bugcounting/nezoba/hw/pics/case_black_bottom_inside.jpg

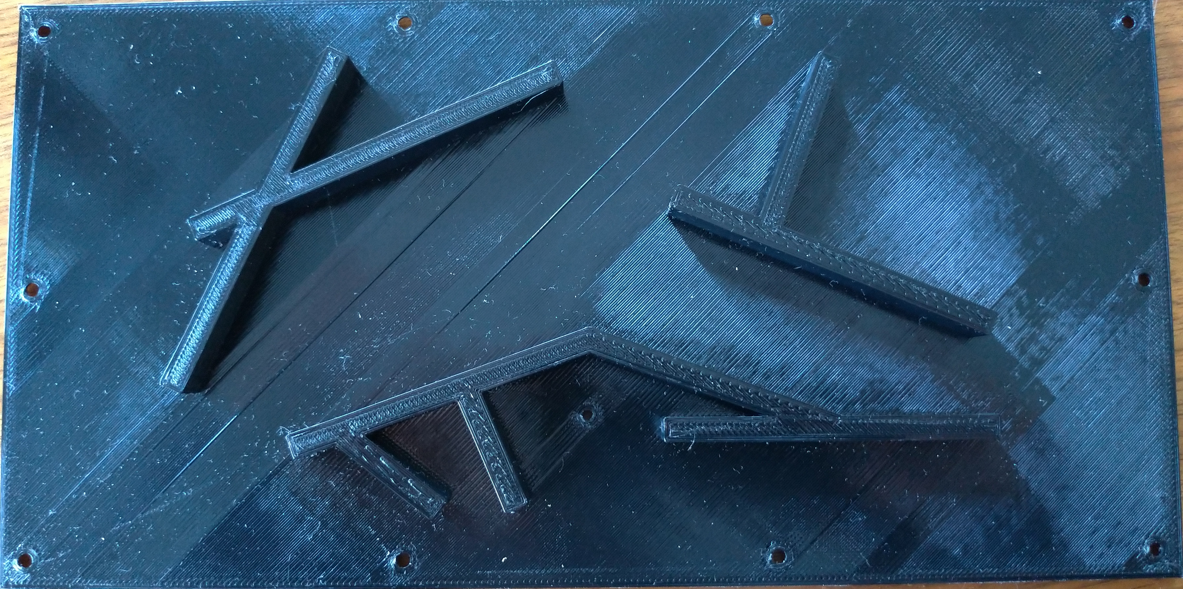
hw/pics/case_black_bottom_inside.jpg
