bugcounting/nezoba/hw/pics/case_black_bottom_outside.jpg

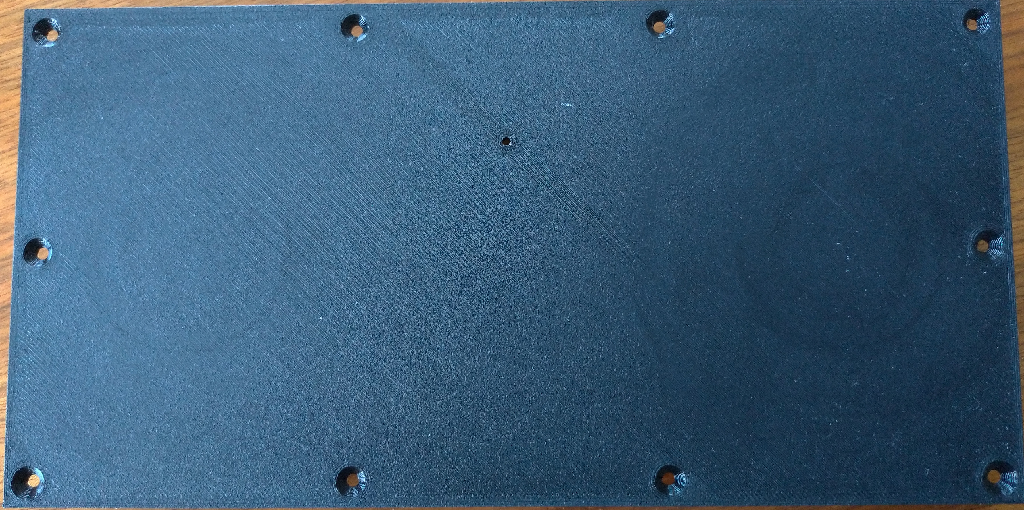
hw/pics/case_black_bottom_outside.jpg
