bugcounting/nezoba/hw/pics/case_orange_bottom_inside.jpg

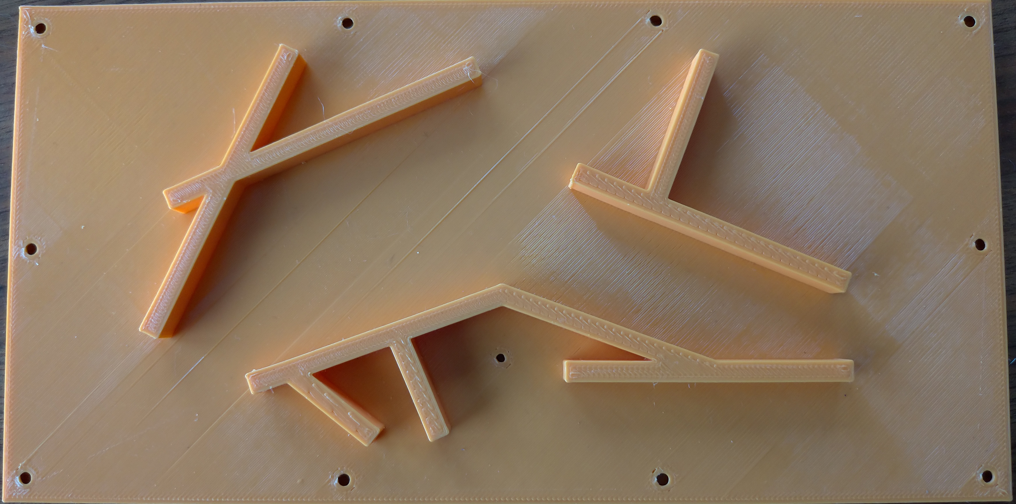
hw/pics/case_orange_bottom_inside.jpg
