bugcounting/nezoba/hw/pics/case_orange_top_inside.jpg

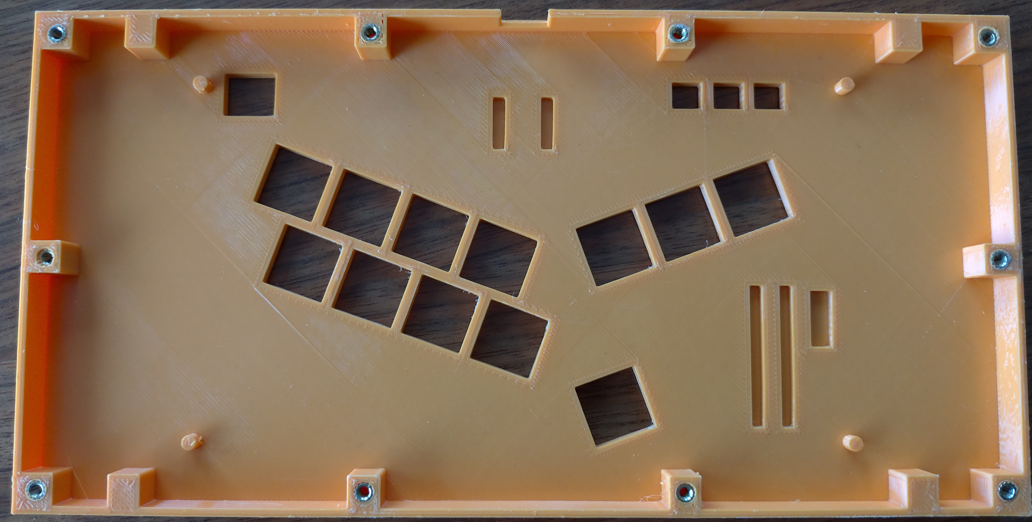
hw/pics/case_orange_top_inside.jpg
