bugcounting/nezoba/hw/pics/case_orange_top_outside.jpg

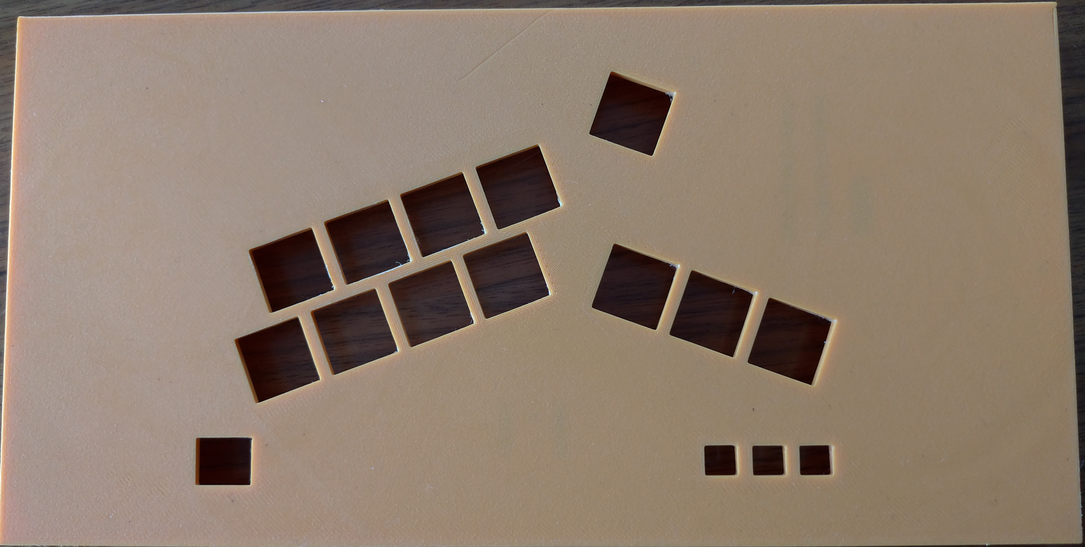
hw/pics/case_orange_top_outside.jpg
