bugcounting/nezoba/hw/pics/NezOba_orange_front.jpg

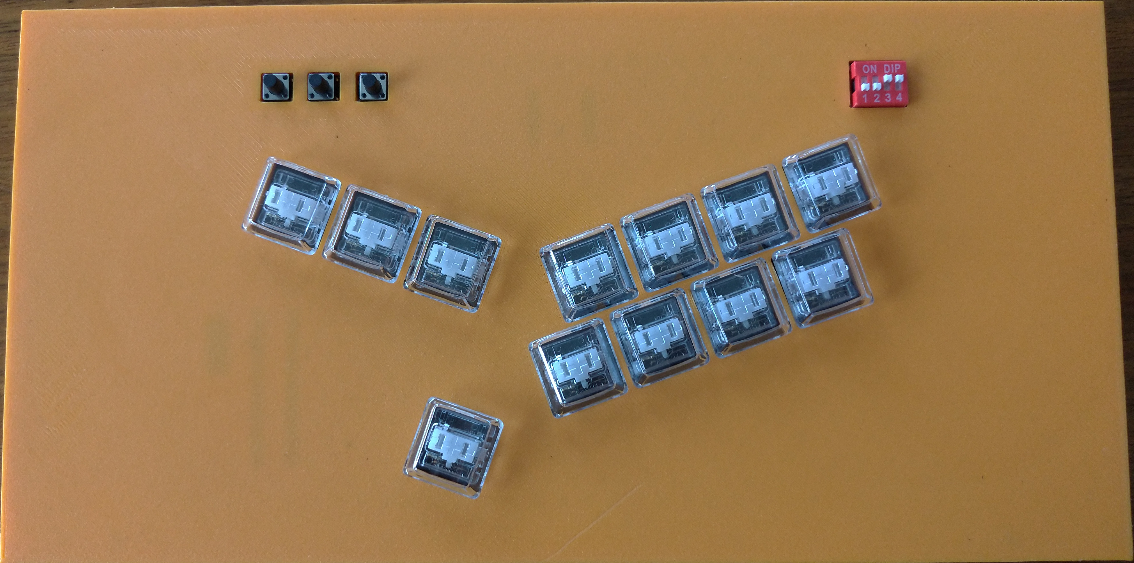
hw/pics/NezOba_orange_front.jpg
