bugcounting/nezoba/hw/pics/PCB_back.jpg

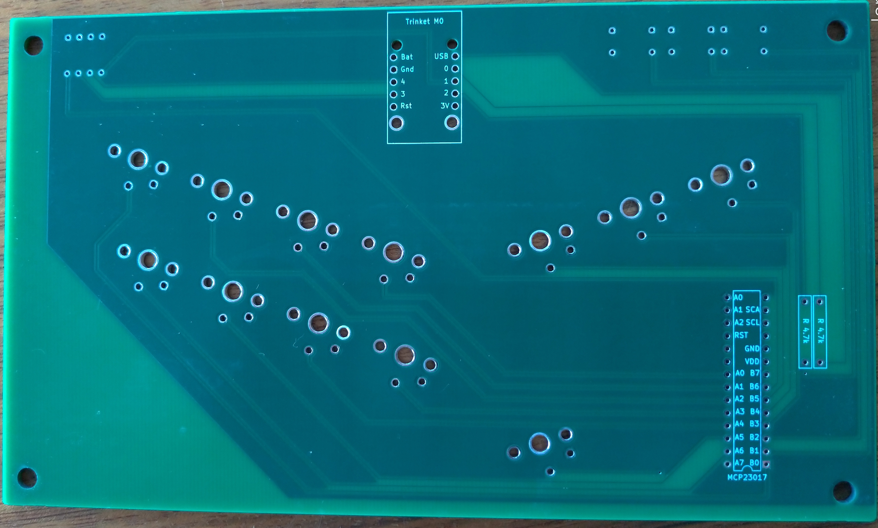
hw/pics/PCB_back.jpg
