bugcounting/nezoba/src/board/remap00.h

/*
  SMM2 standard: Index finger on run (Y), middle finger on jump (B);
  you can choose whether you prefer to spin jump with the thumb (L) or
  with the ring finger (R). Using the thumb should work better if you
  need to quickly switch between regular jumping and spin jumping. You
  can also use the lower row of keys (X, A, ZR), if you find a lower
  stance more comfortable.
*/

// NS
{
   /* ⇐ */       K_DP_LEFT,   K_NOOP,   K_NOOP,
   /* ⇓ */       K_DP_DOWN,   K_NOOP,   K_NOOP,
   /* ⇒ */      K_DP_RIGHT,   K_NOOP,   K_NOOP,
   /* ⇑ */         K_DP_UP,   K_NOOP,   K_NOOP,
   /* Y */             K_Y,   K_NOOP,   K_NOOP,
   /* B */             K_B,   K_NOOP,   K_NOOP,
   /* R */             K_R,   K_NOOP,   K_NOOP,
   /* ZL */           K_ZL,   K_NOOP,   K_NOOP,
   /* L */             K_L,   K_NOOP,   K_NOOP,
   /* X */             K_X,   K_NOOP,   K_NOOP,
   /* A */             K_A,   K_NOOP,   K_NOOP,
   /* ZR */           K_ZR,   K_NOOP,   K_NOOP,
   /* - */         K_MINUS,   K_NOOP,   K_NOOP,
   /* + */          K_PLUS,   K_NOOP,   K_NOOP,
   /* ⌂ */          K_HOME,   K_NOOP,   K_NOOP
}
