bugcounting/nezoba/src/board/remap01.h

/*
  SMM2 run on middle: A variant of "SMM2 standard" for those who
  prefer to use the middle finger to hold run (Y), while using the
  index finger to jump (B). The lower row is the same in "SMM2
  standard", so that you can try both schemes if you are on the fence
  about which one you prefer.
*/

// NS
{
   /* ⇐ */       K_DP_LEFT,   K_NOOP,   K_NOOP,
   /* ⇓ */       K_DP_DOWN,   K_NOOP,   K_NOOP,
   /* ⇒ */      K_DP_RIGHT,   K_NOOP,   K_NOOP,
   /* ⇑ */         K_DP_UP,   K_NOOP,   K_NOOP,
   /* B */             K_B,   K_NOOP,   K_NOOP,
   /* Y */             K_Y,   K_NOOP,   K_NOOP,
   /* R */             K_R,   K_NOOP,   K_NOOP,
   /* ZL */           K_ZL,   K_NOOP,   K_NOOP,
   /* L */             K_L,   K_NOOP,   K_NOOP,
   /* X */             K_X,   K_NOOP,   K_NOOP,
   /* A */             K_A,   K_NOOP,   K_NOOP,
   /* ZR */           K_ZR,   K_NOOP,   K_NOOP,
   /* - */         K_MINUS,   K_NOOP,   K_NOOP,
   /* + */          K_PLUS,   K_NOOP,   K_NOOP,
   /* ⌂ */          K_HOME,   K_NOOP,   K_NOOP
}
