bugcounting/nezoba/src/board/remap02.h

/*
  SMM2 button mashing: For levels that require to spam the B button or
  the Y button. If you need to just mash them, you can use equivalent
  buttons: index and thumb for the run button (Y/X) or middle and
  thumb for the jump button (B/A). This setup also allows you to hold
  run (Y) while also firing with X, which is useful to fire quickly
  without losing speed.
*/

// NS
{
   /* ⇐ */       K_DP_LEFT,   K_NOOP,   K_NOOP,
   /* ⇓ */       K_DP_DOWN,   K_NOOP,   K_NOOP,
   /* ⇒ */      K_DP_RIGHT,   K_NOOP,   K_NOOP,
   /* ⇑ */         K_DP_UP,   K_NOOP,   K_NOOP,
   /* Y */             K_Y,   K_NOOP,   K_NOOP,
   /* B */             K_B,   K_NOOP,   K_NOOP,
   /* R */             K_R,   K_NOOP,   K_NOOP,
   /* L */             K_L,   K_NOOP,   K_NOOP,
   /* X' */           -K_X,   K_NOOP,   K_NOOP,
   /* A' */           -K_A,   K_NOOP,   K_NOOP,
   /* ZL */           K_ZL,   K_NOOP,   K_NOOP,
   /* ZR */           K_ZR,   K_NOOP,   K_NOOP,
   /* - */         K_MINUS,   K_NOOP,   K_NOOP,
   /* + */          K_PLUS,   K_NOOP,   K_NOOP,
   /* ⌂ */          K_HOME,   K_NOOP,   K_NOOP
}
