bugcounting/nezoba/src/board/remap04.h

/*
  SMW standard: This is the equivalent of "SMM2 standard" for Super
  Mario World (as played, for example, on SNES online), which uses A
  instead of L/R/ZL/ZR for spin jumping. Keys A and B appear twice to
  support spin jumping with the ring finger or the thumb, and to use
  the lower row of keys as well as the upper one. ZL and ZR are still
  available, since they are used to suspend the game when playing in
  SNES online.
*/

// NS
{
   /* ⇐ */       K_DP_LEFT,   K_NOOP,   K_NOOP,
   /* ⇓ */       K_DP_DOWN,   K_NOOP,   K_NOOP,
   /* ⇒ */      K_DP_RIGHT,   K_NOOP,   K_NOOP,
   /* ⇑ */         K_DP_UP,   K_NOOP,   K_NOOP,
   /* Y */             K_Y,   K_NOOP,   K_NOOP,
   /* B */             K_B,   K_NOOP,   K_NOOP,
   /* A */             K_A,   K_NOOP,   K_NOOP,
   /* ZL */           K_ZL,   K_NOOP,   K_NOOP,
   /* A */             K_A,   K_NOOP,   K_NOOP,
   /* X */             K_X,   K_NOOP,   K_NOOP,
   /* B */             K_B,   K_NOOP,   K_NOOP,
   /* ZR */           K_ZR,   K_NOOP,   K_NOOP,
   /* - */         K_MINUS,   K_NOOP,   K_NOOP,
   /* + */          K_PLUS,   K_NOOP,   K_NOOP,
   /* ⌂ */          K_HOME,   K_NOOP,   K_NOOP
}
