bugcounting/nezoba/src/board/remap05.h

/*
  NS plain: This is the (more or less) standard button layout of
  arcade sticks on the Nintendo Switch.
*/

// NS
{
   /* ⇐ */       K_DP_LEFT,   K_NOOP,   K_NOOP,
   /* ⇓ */       K_DP_DOWN,   K_NOOP,   K_NOOP,
   /* ⇒ */      K_DP_RIGHT,   K_NOOP,   K_NOOP,
   /* ⇑ */         K_DP_UP,   K_NOOP,   K_NOOP,
   /* X */             K_X,   K_NOOP,   K_NOOP,
   /* Y */             K_Y,   K_NOOP,   K_NOOP,
   /* ZL */           K_ZL,   K_NOOP,   K_NOOP,
   /* ZR */           K_ZR,   K_NOOP,   K_NOOP,
   /* A */             K_A,   K_NOOP,   K_NOOP,
   /* B */             K_B,   K_NOOP,   K_NOOP,
   /* L */             K_L,   K_NOOP,   K_NOOP,
   /* R */             K_R,   K_NOOP,   K_NOOP,
   /* - */         K_MINUS,   K_NOOP,   K_NOOP,
   /* + */          K_PLUS,   K_NOOP,   K_NOOP,
   /* ⌂ */          K_HOME,   K_NOOP,   K_NOOP
}
