bugcounting/nezoba/src/board/remap06.h

/*
  PC plain: This is the (more or less) standard button layout of
  arcade sticks on a PC.
*/

// PC
{
   /* ⇐ */           K_DP_LEFT,   K_NOOP,   K_NOOP,
   /* ⇓ */           K_DP_DOWN,   K_NOOP,   K_NOOP,
   /* ⇒ */          K_DP_RIGHT,   K_NOOP,   K_NOOP,
   /* ⇑ */             K_DP_UP,   K_NOOP,   K_NOOP,
   /* X */                 K_Y,   K_NOOP,   K_NOOP,
   /* Y */                 K_X,   K_NOOP,   K_NOOP,
   /* LT */               K_ZL,   K_NOOP,   K_NOOP,
   /* RT */               K_ZR,   K_NOOP,   K_NOOP,
   /* A */                 K_B,   K_NOOP,   K_NOOP,
   /* B */                 K_A,   K_NOOP,   K_NOOP,
   /* LB */                K_L,   K_NOOP,   K_NOOP,
   /* RB */                K_R,   K_NOOP,   K_NOOP,
   /* select */        K_MINUS,   K_NOOP,   K_NOOP,
   /* start */          K_PLUS,   K_NOOP,   K_NOOP,
   /* ⌂ */              K_HOME,   K_NOOP,   K_NOOP
}
