bugcounting/nezoba/src/board/remap08.h

/*
  Levelhead standard: For playing Levelhead on the Nintendo Switch.
  Use the index finger to jump (B), the middle finger to grab (ZR),
  and the thumb or ring finger for special actions (when you have a
  powerup). Holding L restarts the level at the latest checkpoint. The
  rest of the remapping adds keys X, Y, and R for menu navigation,
  even though they are not used while playing.
*/

// NS
{
   /* ⇐ */       K_DP_LEFT,   K_NOOP,   K_NOOP,
   /* ⇓ */       K_DP_DOWN,   K_NOOP,   K_NOOP,
   /* ⇒ */      K_DP_RIGHT,   K_NOOP,   K_NOOP,
   /* ⇑ */         K_DP_UP,   K_NOOP,   K_NOOP,
   /* B */             K_B,   K_NOOP,   K_NOOP,
   /* ZR */           K_ZR,   K_NOOP,   K_NOOP,
   /* A */             K_A,   K_NOOP,   K_NOOP,
   /* L */             K_L,   K_NOOP,   K_NOOP,
   /* A */             K_A,   K_NOOP,   K_NOOP,
   /* X */             K_X,   K_NOOP,   K_NOOP,
   /* Y */             K_Y,   K_NOOP,   K_NOOP,
   /* R */             K_R,   K_NOOP,   K_NOOP,
   /* - */         K_MINUS,   K_NOOP,   K_NOOP,
   /* + */          K_PLUS,   K_NOOP,   K_NOOP,
   /* ⌂ */          K_HOME,   K_NOOP,   K_NOOP
}
