bugcounting/nezoba/src/board/remap11.h

/*

*/

// 
{
        K_NOOP,   K_NOOP,   K_NOOP,
        K_NOOP,   K_NOOP,   K_NOOP,
        K_NOOP,   K_NOOP,   K_NOOP,
        K_NOOP,   K_NOOP,   K_NOOP,
        K_NOOP,   K_NOOP,   K_NOOP,
        K_NOOP,   K_NOOP,   K_NOOP,
        K_NOOP,   K_NOOP,   K_NOOP,
        K_NOOP,   K_NOOP,   K_NOOP,
        K_NOOP,   K_NOOP,   K_NOOP,
        K_NOOP,   K_NOOP,   K_NOOP,
        K_NOOP,   K_NOOP,   K_NOOP,
        K_NOOP,   K_NOOP,   K_NOOP,
        K_NOOP,   K_NOOP,   K_NOOP,
        K_NOOP,   K_NOOP,   K_NOOP,
        K_NOOP,   K_NOOP,   K_NOOP
}
